tmolteno/zl4aa/sdr/sdr_code/include/oled_min.h

// ===================================================================================
// SSD1306 128x64 Pixels OLED Minimal Functions                               * v1.0 *
// ===================================================================================
//
// Collection of the most necessary functions for controlling an SSD1306 128x64 pixels
// I2C OLED.
//
// References:
// -----------
// - TinyOLEDdemo: https://github.com/wagiminator/attiny13-tinyoleddemo
// - Neven Boyanov: https://github.com/tinusaur/ssd1306xled
// - Stephen Denne: https://github.com/datacute/Tiny4kOLED
//
// 2022 by Stefan Wagner: https://github.com/wagiminator

#pragma once

#ifdef __cplusplus
extern "C" {
#endif

#include "i2c_tx.h"

// OLED definitions
#define OLED_ADDR         0x3C    // OLED write address (0x3C << 1)
#define OLED_CMD_MODE     0x00    // set command mode
#define OLED_DAT_MODE     0x40    // set data mode

// OLED commands
#define OLED_COLUMN_LOW   0x00    // set lower 4 bits of start column (0x00 - 0x0F)
#define OLED_COLUMN_HIGH  0x10    // set higher 4 bits of start column (0x10 - 0x1F)
#define OLED_MEMORYMODE   0x20    // set memory addressing mode (following byte)
#define OLED_COLUMNS      0x21    // set start and end column (following 2 bytes)
#define OLED_PAGES        0x22    // set start and end page (following 2 bytes)
#define OLED_SCROLL_OFF   0x2E    // deactivate scroll command
#define OLED_STARTLINE    0x40    // set display start line (0x40-0x7F = 0-63)
#define OLED_CONTRAST     0x81    // set display contrast (following byte)
#define OLED_CHARGEPUMP   0x8D    // (following byte - 0x14:enable, 0x10: disable)
#define OLED_XFLIP_OFF    0xA0    // don't flip display horizontally
#define OLED_XFLIP        0xA1    // flip display horizontally
#define OLED_INVERT_OFF   0xA6    // set non-inverted display
#define OLED_INVERT       0xA7    // set inverse display
#define OLED_MULTIPLEX    0xA8    // set multiplex ratio (following byte)
#define OLED_DISPLAY_OFF  0xAE    // set display off (sleep mode)
#define OLED_DISPLAY_ON   0xAF    // set display on
#define OLED_PAGE         0xB0    // set start page (following byte)
#define OLED_YFLIP_OFF    0xC0    // don't flip display vertically
#define OLED_YFLIP        0xC8    // flip display vertically
#define OLED_OFFSET       0xD3    // set display offset (y-scroll: following byte)
#define OLED_COMPINS      0xDA    // set COM pin config (following byte)

/*
#define OLED_xfer_start     OLED_I2C_start(OLED_ADDR)
#define OLED_xfer_stop      OLED_I2C_stop
#define OLED_send_byte(b)   OLED_I2C_write(b)
#define OLED_data_stop      OLED_I2C_stop
#define OLED_command_stop   OLED_I2C_stop
*/
// Functions
void OLED_init(void);
void OLED_data_start(void);
void OLED_command_start(void);
void OLED_send_command(uint8_t cmd);
void OLED_setpos(uint8_t x, uint8_t y);
void OLED_fill(uint8_t p);
void OLED_draw_bmp(uint8_t x0, uint8_t y0, uint8_t x1, uint8_t y1, const uint8_t* bmp);
void OLED_draw_xbm(const uint8_t * xbm);
void OLED_draw_xbm_vertical(const uint8_t * xbm);

#ifdef __cplusplus
};
#endif
